samscam/clocklet/Website/images/black-sideon.png

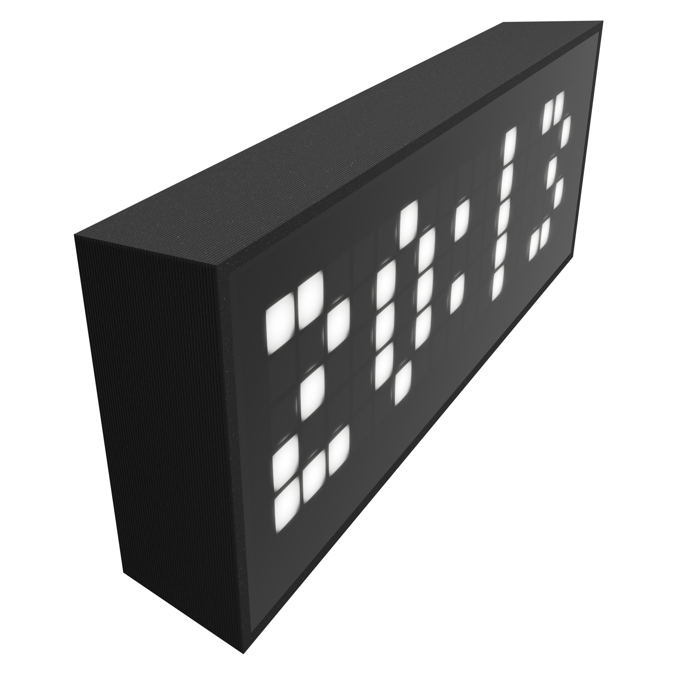
Website/images/black-sideon.png
