samscam/clocklet/Website/images/clocklet5-black-masked.png

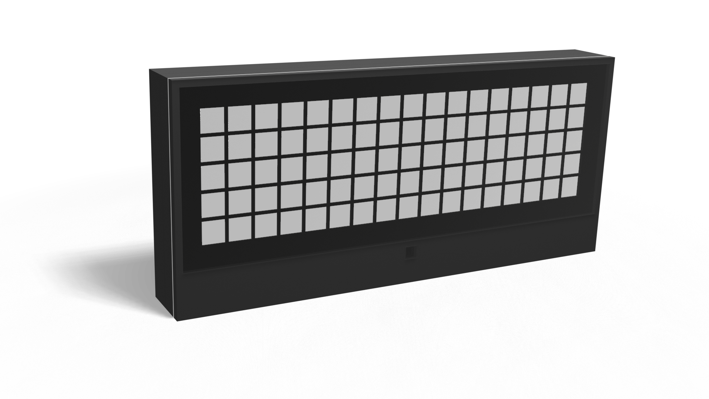
Website/images/clocklet5-black-masked.png
