samscam/clocklet/Website/images/clocklet5-black-time.png

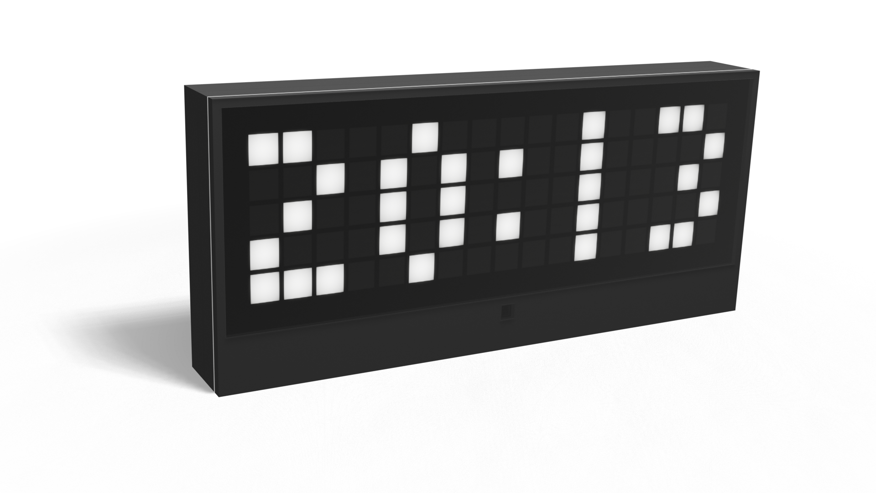
Website/images/clocklet5-black-time.png
