samscam/clocklet/Website/images/clocklet5-final-hello.png

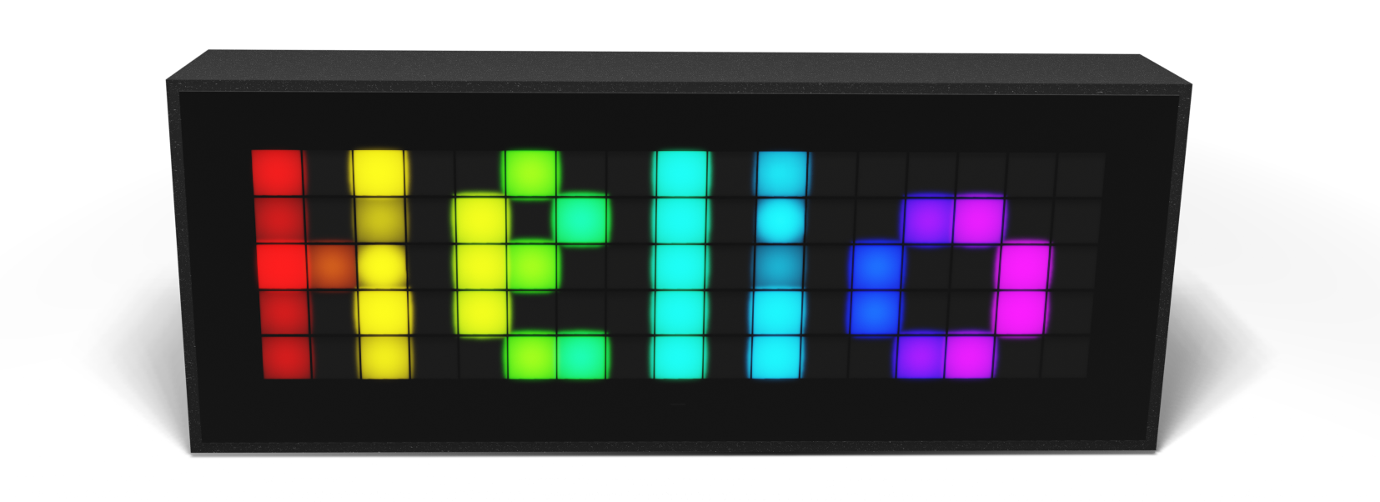
Website/images/clocklet5-final-hello.png
