samscam/clocklet/Embedded/src/TimeThings/Zones.h

#pragma once

const char* zones[] = {
"Africa/Abidjan","GMT0",
"Africa/Accra","GMT0",
"Africa/Addis_Ababa","EAT-3",
"Africa/Algiers","CET-1",
"Africa/Asmara","EAT-3",
"Africa/Bamako","GMT0",
"Africa/Bangui","WAT-1",
"Africa/Banjul","GMT0",
"Africa/Bissau","GMT0",
"Africa/Blantyre","CAT-2",
"Africa/Brazzaville","WAT-1",
"Africa/Bujumbura","CAT-2",
"Africa/Cairo","EET-2",
"Africa/Casablanca","FAKE-1",
"Africa/Ceuta","CET-1CEST,M3.5.0,M10.5.0/3",
"Africa/Conakry","GMT0",
"Africa/Dakar","GMT0",
"Africa/Dar_es_Salaam","EAT-3",
"Africa/Djibouti","EAT-3",
"Africa/Douala","WAT-1",
"Africa/El_Aaiun","FAKE-1",
"Africa/Freetown","GMT0",
"Africa/Gaborone","CAT-2",
"Africa/Harare","CAT-2",
"Africa/Johannesburg","SAST-2",
"Africa/Juba","EAT-3",
"Africa/Kampala","EAT-3",
"Africa/Khartoum","CAT-2",
"Africa/Kigali","CAT-2",
"Africa/Kinshasa","WAT-1",
"Africa/Lagos","WAT-1",
"Africa/Libreville","WAT-1",
"Africa/Lome","GMT0",
"Africa/Luanda","WAT-1",
"Africa/Lubumbashi","CAT-2",
"Africa/Lusaka","CAT-2",
"Africa/Malabo","WAT-1",
"Africa/Maputo","CAT-2",
"Africa/Maseru","SAST-2",
"Africa/Mbabane","SAST-2",
"Africa/Mogadishu","EAT-3",
"Africa/Monrovia","GMT0",
"Africa/Nairobi","EAT-3",
"Africa/Ndjamena","WAT-1",
"Africa/Niamey","WAT-1",
"Africa/Nouakchott","GMT0",
"Africa/Ouagadougou","GMT0",
"Africa/Porto-Novo","WAT-1",
"Africa/Sao_Tome","GMT0",
"Africa/Tripoli","EET-2",
"Africa/Tunis","CET-1",
"Africa/Windhoek","CAT-2",
"America/Adak","HST10HDT,M3.2.0,M11.1.0",
"America/Anchorage","AKST9AKDT,M3.2.0,M11.1.0",
"America/Anguilla","AST4",
"America/Antigua","AST4",
"America/Araguaina","FAKE3",
"America/Argentina/Buenos_Aires","FAKE3",
"America/Argentina/Catamarca","FAKE3",
"America/Argentina/Cordoba","FAKE3",
"America/Argentina/Jujuy","FAKE3",
"America/Argentina/La_Rioja","FAKE3",
"America/Argentina/Mendoza","FAKE3",
"America/Argentina/Rio_Gallegos","FAKE3",
"America/Argentina/Salta","FAKE3",
"America/Argentina/San_Juan","FAKE3",
"America/Argentina/San_Luis","FAKE3",
"America/Argentina/Tucuman","FAKE3",
"America/Argentina/Ushuaia","FAKE3",
"America/Aruba","AST4",
"America/Asuncion","FAKE4FAKE,M10.1.0/0,M3.4.0/0",
"America/Atikokan","EST5",
"America/Bahia","FAKE3",
"America/Bahia_Banderas","CST6CDT,M4.1.0,M10.5.0",
"America/Barbados","AST4",
"America/Belem","FAKE3",
"America/Belize","CST6",
"America/Blanc-Sablon","AST4",
"America/Boa_Vista","FAKE4",
"America/Bogota","FAKE5",
"America/Boise","MST7MDT,M3.2.0,M11.1.0",
"America/Cambridge_Bay","MST7MDT,M3.2.0,M11.1.0",
"America/Campo_Grande","FAKE4",
"America/Cancun","EST5",
"America/Caracas","FAKE4",
"America/Cayenne","FAKE3",
"America/Cayman","EST5",
"America/Chicago","CST6CDT,M3.2.0,M11.1.0",
"America/Chihuahua","MST7MDT,M4.1.0,M10.5.0",
"America/Costa_Rica","CST6",
"America/Creston","MST7",
"America/Cuiaba","FAKE4",
"America/Curacao","AST4",
"America/Danmarkshavn","GMT0",
"America/Dawson","MST7",
"America/Dawson_Creek","MST7",
"America/Denver","MST7MDT,M3.2.0,M11.1.0",
"America/Detroit","EST5EDT,M3.2.0,M11.1.0",
"America/Dominica","AST4",
"America/Edmonton","MST7MDT,M3.2.0,M11.1.0",
"America/Eirunepe","FAKE5",
"America/El_Salvador","CST6",
"America/Fortaleza","FAKE3",
"America/Fort_Nelson","MST7",
"America/Glace_Bay","AST4ADT,M3.2.0,M11.1.0",
"America/Godthab","FAKE3FAKE,M3.5.0/-2,M10.5.0/-1",
"America/Goose_Bay","AST4ADT,M3.2.0,M11.1.0",
"America/Grand_Turk","EST5EDT,M3.2.0,M11.1.0",
"America/Grenada","AST4",
"America/Guadeloupe","AST4",
"America/Guatemala","CST6",
"America/Guayaquil","FAKE5",
"America/Guyana","FAKE4",
"America/Halifax","AST4ADT,M3.2.0,M11.1.0",
"America/Havana","CST5CDT,M3.2.0/0,M11.1.0/1",
"America/Hermosillo","MST7",
"America/Indiana/Indianapolis","EST5EDT,M3.2.0,M11.1.0",
"America/Indiana/Knox","CST6CDT,M3.2.0,M11.1.0",
"America/Indiana/Marengo","EST5EDT,M3.2.0,M11.1.0",
"America/Indiana/Petersburg","EST5EDT,M3.2.0,M11.1.0",
"America/Indiana/Tell_City","CST6CDT,M3.2.0,M11.1.0",
"America/Indiana/Vevay","EST5EDT,M3.2.0,M11.1.0",
"America/Indiana/Vincennes","EST5EDT,M3.2.0,M11.1.0",
"America/Indiana/Winamac","EST5EDT,M3.2.0,M11.1.0",
"America/Inuvik","MST7MDT,M3.2.0,M11.1.0",
"America/Iqaluit","EST5EDT,M3.2.0,M11.1.0",
"America/Jamaica","EST5",
"America/Juneau","AKST9AKDT,M3.2.0,M11.1.0",
"America/Kentucky/Louisville","EST5EDT,M3.2.0,M11.1.0",
"America/Kentucky/Monticello","EST5EDT,M3.2.0,M11.1.0",
"America/Kralendijk","AST4",
"America/La_Paz","FAKE4",
"America/Lima","FAKE5",
"America/Los_Angeles","PST8PDT,M3.2.0,M11.1.0",
"America/Lower_Princes","AST4",
"America/Maceio","FAKE3",
"America/Managua","CST6",
"America/Manaus","FAKE4",
"America/Marigot","AST4",
"America/Martinique","AST4",
"America/Matamoros","CST6CDT,M3.2.0,M11.1.0",
"America/Mazatlan","MST7MDT,M4.1.0,M10.5.0",
"America/Menominee","CST6CDT,M3.2.0,M11.1.0",
"America/Merida","CST6CDT,M4.1.0,M10.5.0",
"America/Metlakatla","AKST9AKDT,M3.2.0,M11.1.0",
"America/Mexico_City","CST6CDT,M4.1.0,M10.5.0",
"America/Miquelon","FAKE3FAKE,M3.2.0,M11.1.0",
"America/Moncton","AST4ADT,M3.2.0,M11.1.0",
"America/Monterrey","CST6CDT,M4.1.0,M10.5.0",
"America/Montevideo","FAKE3",
"America/Montreal","EST5EDT,M3.2.0,M11.1.0",
"America/Montserrat","AST4",
"America/Nassau","EST5EDT,M3.2.0,M11.1.0",
"America/New_York","EST5EDT,M3.2.0,M11.1.0",
"America/Nipigon","EST5EDT,M3.2.0,M11.1.0",
"America/Nome","AKST9AKDT,M3.2.0,M11.1.0",
"America/Noronha","FAKE2",
"America/North_Dakota/Beulah","CST6CDT,M3.2.0,M11.1.0",
"America/North_Dakota/Center","CST6CDT,M3.2.0,M11.1.0",
"America/North_Dakota/New_Salem","CST6CDT,M3.2.0,M11.1.0",
"America/Ojinaga","MST7MDT,M3.2.0,M11.1.0",
"America/Panama","EST5",
"America/Pangnirtung","EST5EDT,M3.2.0,M11.1.0",
"America/Paramaribo","FAKE3",
"America/Phoenix","MST7",
"America/Port-au-Prince","EST5EDT,M3.2.0,M11.1.0",
"America/Port_of_Spain","AST4",
"America/Porto_Velho","FAKE4",
"America/Puerto_Rico","AST4",
"America/Punta_Arenas","FAKE3",
"America/Rainy_River","CST6CDT,M3.2.0,M11.1.0",
"America/Rankin_Inlet","CST6CDT,M3.2.0,M11.1.0",
"America/Recife","FAKE3",
"America/Regina","CST6",
"America/Resolute","CST6CDT,M3.2.0,M11.1.0",
"America/Rio_Branco","FAKE5",
"America/Santarem","FAKE3",
"America/Santiago","FAKE4FAKE,M9.1.6/24,M4.1.6/24",
"America/Santo_Domingo","AST4",
"America/Sao_Paulo","FAKE3",
"America/Scoresbysund","FAKE1FAKE,M3.5.0/0,M10.5.0/1",
"America/Sitka","AKST9AKDT,M3.2.0,M11.1.0",
"America/St_Barthelemy","AST4",
"America/St_Johns","NST3:30NDT,M3.2.0,M11.1.0",
"America/St_Kitts","AST4",
"America/St_Lucia","AST4",
"America/St_Thomas","AST4",
"America/St_Vincent","AST4",
"America/Swift_Current","CST6",
"America/Tegucigalpa","CST6",
"America/Thule","AST4ADT,M3.2.0,M11.1.0",
"America/Thunder_Bay","EST5EDT,M3.2.0,M11.1.0",
"America/Tijuana","PST8PDT,M3.2.0,M11.1.0",
"America/Toronto","EST5EDT,M3.2.0,M11.1.0",
"America/Tortola","AST4",
"America/Vancouver","PST8PDT,M3.2.0,M11.1.0",
"America/Whitehorse","MST7",
"America/Winnipeg","CST6CDT,M3.2.0,M11.1.0",
"America/Yakutat","AKST9AKDT,M3.2.0,M11.1.0",
"America/Yellowknife","MST7MDT,M3.2.0,M11.1.0",
"Antarctica/Casey","FAKE-8",
"Antarctica/Davis","FAKE-7",
"Antarctica/DumontDUrville","FAKE-10",
"Antarctica/Macquarie","FAKE-11",
"Antarctica/Mawson","FAKE-5",
"Antarctica/McMurdo","NZST-12NZDT,M9.5.0,M4.1.0/3",
"Antarctica/Palmer","FAKE3",
"Antarctica/Rothera","FAKE3",
"Antarctica/Syowa","FAKE-3",
"Antarctica/Troll","FAKE0FAKE-2,M3.5.0/1,M10.5.0/3",
"Antarctica/Vostok","FAKE-6",
"Arctic/Longyearbyen","CET-1CEST,M3.5.0,M10.5.0/3",
"Asia/Aden","FAKE-3",
"Asia/Almaty","FAKE-6",
"Asia/Amman","EET-2EEST,M3.5.4/24,M10.5.5/1",
"Asia/Anadyr","FAKE-12",
"Asia/Aqtau","FAKE-5",
"Asia/Aqtobe","FAKE-5",
"Asia/Ashgabat","FAKE-5",
"Asia/Atyrau","FAKE-5",
"Asia/Baghdad","FAKE-3",
"Asia/Bahrain","FAKE-3",
"Asia/Baku","FAKE-4",
"Asia/Bangkok","FAKE-7",
"Asia/Barnaul","FAKE-7",
"Asia/Beirut","EET-2EEST,M3.5.0/0,M10.5.0/0",
"Asia/Bishkek","FAKE-6",
"Asia/Brunei","FAKE-8",
"Asia/Chita","FAKE-9",
"Asia/Choibalsan","FAKE-8",
"Asia/Colombo","FAKE-5:30",
"Asia/Damascus","EET-2EEST,M3.5.5/0,M10.5.5/0",
"Asia/Dhaka","FAKE-6",
"Asia/Dili","FAKE-9",
"Asia/Dubai","FAKE-4",
"Asia/Dushanbe","FAKE-5",
"Asia/Famagusta","EET-2EEST,M3.5.0/3,M10.5.0/4",
"Asia/Gaza","EET-2EEST,M3.5.5/0,M10.5.6/1",
"Asia/Hebron","EET-2EEST,M3.5.5/0,M10.5.6/1",
"Asia/Ho_Chi_Minh","FAKE-7",
"Asia/Hong_Kong","HKT-8",
"Asia/Hovd","FAKE-7",
"Asia/Irkutsk","FAKE-8",
"Asia/Jakarta","WIB-7",
"Asia/Jayapura","WIT-9",
"Asia/Jerusalem","IST-2IDT,M3.4.4/26,M10.5.0",
"Asia/Kabul","FAKE-4:30",
"Asia/Kamchatka","FAKE-12",
"Asia/Karachi","PKT-5",
"Asia/Kathmandu","FAKE-5:45",
"Asia/Khandyga","FAKE-9",
"Asia/Kolkata","IST-5:30",
"Asia/Krasnoyarsk","FAKE-7",
"Asia/Kuala_Lumpur","FAKE-8",
"Asia/Kuching","FAKE-8",
"Asia/Kuwait","FAKE-3",
"Asia/Macau","CST-8",
"Asia/Magadan","FAKE-11",
"Asia/Makassar","WITA-8",
"Asia/Manila","PST-8",
"Asia/Muscat","FAKE-4",
"Asia/Nicosia","EET-2EEST,M3.5.0/3,M10.5.0/4",
"Asia/Novokuznetsk","FAKE-7",
"Asia/Novosibirsk","FAKE-7",
"Asia/Omsk","FAKE-6",
"Asia/Oral","FAKE-5",
"Asia/Phnom_Penh","FAKE-7",
"Asia/Pontianak","WIB-7",
"Asia/Pyongyang","KST-9",
"Asia/Qatar","FAKE-3",
"Asia/Qyzylorda","FAKE-5",
"Asia/Riyadh","FAKE-3",
"Asia/Sakhalin","FAKE-11",
"Asia/Samarkand","FAKE-5",
"Asia/Seoul","KST-9",
"Asia/Shanghai","CST-8",
"Asia/Singapore","FAKE-8",
"Asia/Srednekolymsk","FAKE-11",
"Asia/Taipei","CST-8",
"Asia/Tashkent","FAKE-5",
"Asia/Tbilisi","FAKE-4",
"Asia/Tehran","FAKE-3:30FAKE,J79/24,J263/24",
"Asia/Thimphu","FAKE-6",
"Asia/Tokyo","JST-9",
"Asia/Tomsk","FAKE-7",
"Asia/Ulaanbaatar","FAKE-8",
"Asia/Urumqi","FAKE-6",
"Asia/Ust-Nera","FAKE-10",
"Asia/Vientiane","FAKE-7",
"Asia/Vladivostok","FAKE-10",
"Asia/Yakutsk","FAKE-9",
"Asia/Yangon","FAKE-6:30",
"Asia/Yekaterinburg","FAKE-5",
"Asia/Yerevan","FAKE-4",
"Atlantic/Azores","FAKE1FAKE,M3.5.0/0,M10.5.0/1",
"Atlantic/Bermuda","AST4ADT,M3.2.0,M11.1.0",
"Atlantic/Canary","WET0WEST,M3.5.0/1,M10.5.0",
"Atlantic/Cape_Verde","FAKE1",
"Atlantic/Faroe","WET0WEST,M3.5.0/1,M10.5.0",
"Atlantic/Madeira","WET0WEST,M3.5.0/1,M10.5.0",
"Atlantic/Reykjavik","GMT0",
"Atlantic/South_Georgia","FAKE2",
"Atlantic/Stanley","FAKE3",
"Atlantic/St_Helena","GMT0",
"Australia/Adelaide","ACST-9:30ACDT,M10.1.0,M4.1.0/3",
"Australia/Brisbane","AEST-10",
"Australia/Broken_Hill","ACST-9:30ACDT,M10.1.0,M4.1.0/3",
"Australia/Currie","AEST-10AEDT,M10.1.0,M4.1.0/3",
"Australia/Darwin","ACST-9:30",
"Australia/Eucla","FAKE-8:45",
"Australia/Hobart","AEST-10AEDT,M10.1.0,M4.1.0/3",
"Australia/Lindeman","AEST-10",
"Australia/Lord_Howe","FAKE-10:30FAKE-11,M10.1.0,M4.1.0",
"Australia/Melbourne","AEST-10AEDT,M10.1.0,M4.1.0/3",
"Australia/Perth","AWST-8",
"Australia/Sydney","AEST-10AEDT,M10.1.0,M4.1.0/3",
"Europe/Amsterdam","CET-1CEST,M3.5.0,M10.5.0/3",
"Europe/Andorra","CET-1CEST,M3.5.0,M10.5.0/3",
"Europe/Astrakhan","FAKE-4",
"Europe/Athens","EET-2EEST,M3.5.0/3,M10.5.0/4",
"Europe/Belgrade","CET-1CEST,M3.5.0,M10.5.0/3",
"Europe/Berlin","CET-1CEST,M3.5.0,M10.5.0/3",
"Europe/Bratislava","CET-1CEST,M3.5.0,M10.5.0/3",
"Europe/Brussels","CET-1CEST,M3.5.0,M10.5.0/3",
"Europe/Bucharest","EET-2EEST,M3.5.0/3,M10.5.0/4",
"Europe/Budapest","CET-1CEST,M3.5.0,M10.5.0/3",
"Europe/Busingen","CET-1CEST,M3.5.0,M10.5.0/3",
"Europe/Chisinau","EET-2EEST,M3.5.0,M10.5.0/3",
"Europe/Copenhagen","CET-1CEST,M3.5.0,M10.5.0/3",
"Europe/Dublin","IST-1GMT0,M10.5.0,M3.5.0/1",
"Europe/Gibraltar","CET-1CEST,M3.5.0,M10.5.0/3",
"Europe/Guernsey","GMT0BST,M3.5.0/1,M10.5.0",
"Europe/Helsinki","EET-2EEST,M3.5.0/3,M10.5.0/4",
"Europe/Isle_of_Man","GMT0BST,M3.5.0/1,M10.5.0",
"Europe/Istanbul","FAKE-3",
"Europe/Jersey","GMT0BST,M3.5.0/1,M10.5.0",
"Europe/Kaliningrad","EET-2",
"Europe/Kiev","EET-2EEST,M3.5.0/3,M10.5.0/4",
"Europe/Kirov","FAKE-3",
"Europe/Lisbon","WET0WEST,M3.5.0/1,M10.5.0",
"Europe/Ljubljana","CET-1CEST,M3.5.0,M10.5.0/3",
"Europe/London","GMT0BST,M3.5.0/1,M10.5.0",
"Europe/Luxembourg","CET-1CEST,M3.5.0,M10.5.0/3",
"Europe/Madrid","CET-1CEST,M3.5.0,M10.5.0/3",
"Europe/Malta","CET-1CEST,M3.5.0,M10.5.0/3",
"Europe/Mariehamn","EET-2EEST,M3.5.0/3,M10.5.0/4",
"Europe/Minsk","FAKE-3",
"Europe/Monaco","CET-1CEST,M3.5.0,M10.5.0/3",
"Europe/Moscow","MSK-3",
"Europe/Oslo","CET-1CEST,M3.5.0,M10.5.0/3",
"Europe/Paris","CET-1CEST,M3.5.0,M10.5.0/3",
"Europe/Podgorica","CET-1CEST,M3.5.0,M10.5.0/3",
"Europe/Prague","CET-1CEST,M3.5.0,M10.5.0/3",
"Europe/Riga","EET-2EEST,M3.5.0/3,M10.5.0/4",
"Europe/Rome","CET-1CEST,M3.5.0,M10.5.0/3",
"Europe/Samara","FAKE-4",
"Europe/San_Marino","CET-1CEST,M3.5.0,M10.5.0/3",
"Europe/Sarajevo","CET-1CEST,M3.5.0,M10.5.0/3",
"Europe/Saratov","FAKE-4",
"Europe/Simferopol","MSK-3",
"Europe/Skopje","CET-1CEST,M3.5.0,M10.5.0/3",
"Europe/Sofia","EET-2EEST,M3.5.0/3,M10.5.0/4",
"Europe/Stockholm","CET-1CEST,M3.5.0,M10.5.0/3",
"Europe/Tallinn","EET-2EEST,M3.5.0/3,M10.5.0/4",
"Europe/Tirane","CET-1CEST,M3.5.0,M10.5.0/3",
"Europe/Ulyanovsk","FAKE-4",
"Europe/Uzhgorod","EET-2EEST,M3.5.0/3,M10.5.0/4",
"Europe/Vaduz","CET-1CEST,M3.5.0,M10.5.0/3",
"Europe/Vatican","CET-1CEST,M3.5.0,M10.5.0/3",
"Europe/Vienna","CET-1CEST,M3.5.0,M10.5.0/3",
"Europe/Vilnius","EET-2EEST,M3.5.0/3,M10.5.0/4",
"Europe/Volgograd","FAKE-4",
"Europe/Warsaw","CET-1CEST,M3.5.0,M10.5.0/3",
"Europe/Zagreb","CET-1CEST,M3.5.0,M10.5.0/3",
"Europe/Zaporozhye","EET-2EEST,M3.5.0/3,M10.5.0/4",
"Europe/Zurich","CET-1CEST,M3.5.0,M10.5.0/3",
"Indian/Antananarivo","EAT-3",
"Indian/Chagos","FAKE-6",
"Indian/Christmas","FAKE-7",
"Indian/Cocos","FAKE-6:30",
"Indian/Comoro","EAT-3",
"Indian/Kerguelen","FAKE-5",
"Indian/Mahe","FAKE-4",
"Indian/Maldives","FAKE-5",
"Indian/Mauritius","FAKE-4",
"Indian/Mayotte","EAT-3",
"Indian/Reunion","FAKE-4",
"Pacific/Apia","FAKE-13FAKE,M9.5.0/3,M4.1.0/4",
"Pacific/Auckland","NZST-12NZDT,M9.5.0,M4.1.0/3",
"Pacific/Bougainville","FAKE-11",
"Pacific/Chatham","FAKE-12:45FAKE,M9.5.0/2:45,M4.1.0/3:45",
"Pacific/Chuuk","FAKE-10",
"Pacific/Easter","FAKE6FAKE,M9.1.6/22,M4.1.6/22",
"Pacific/Efate","FAKE-11",
"Pacific/Enderbury","FAKE-13",
"Pacific/Fakaofo","FAKE-13",
"Pacific/Fiji","FAKE-12FAKE,M11.2.0,M1.2.3/99",
"Pacific/Funafuti","FAKE-12",
"Pacific/Galapagos","FAKE6",
"Pacific/Gambier","FAKE9",
"Pacific/Guadalcanal","FAKE-11",
"Pacific/Guam","ChST-10",
"Pacific/Honolulu","HST10",
"Pacific/Kiritimati","FAKE-14",
"Pacific/Kosrae","FAKE-11",
"Pacific/Kwajalein","FAKE-12",
"Pacific/Majuro","FAKE-12",
"Pacific/Marquesas","FAKE9:30",
"Pacific/Midway","SST11",
"Pacific/Nauru","FAKE-12",
"Pacific/Niue","FAKE11",
"Pacific/Norfolk","FAKE-11FAKE,M10.1.0,M4.1.0/3",
"Pacific/Noumea","FAKE-11",
"Pacific/Pago_Pago","SST11",
"Pacific/Palau","FAKE-9",
"Pacific/Pitcairn","FAKE8",
"Pacific/Pohnpei","FAKE-11",
"Pacific/Port_Moresby","FAKE-10",
"Pacific/Rarotonga","FAKE10",
"Pacific/Saipan","ChST-10",
"Pacific/Tahiti","FAKE10",
"Pacific/Tarawa","FAKE-12",
"Pacific/Tongatapu","FAKE-13",
"Pacific/Wake","FAKE-12",
"Pacific/Wallis","FAKE-12",
"Etc/GMT","GMT0",
"Etc/GMT-0","GMT0",
"Etc/GMT-1","FAKE-1",
"Etc/GMT-2","FAKE-2",
"Etc/GMT-3","FAKE-3",
"Etc/GMT-4","FAKE-4",
"Etc/GMT-5","FAKE-5",
"Etc/GMT-6","FAKE-6",
"Etc/GMT-7","FAKE-7",
"Etc/GMT-8","FAKE-8",
"Etc/GMT-9","FAKE-9",
"Etc/GMT-10","FAKE-10",
"Etc/GMT-11","FAKE-11",
"Etc/GMT-12","FAKE-12",
"Etc/GMT-13","FAKE-13",
"Etc/GMT-14","FAKE-14",
"Etc/GMT0","GMT0",
"Etc/GMT+0","GMT0",
"Etc/GMT+1","FAKE1",
"Etc/GMT+2","FAKE2",
"Etc/GMT+3","FAKE3",
"Etc/GMT+4","FAKE4",
"Etc/GMT+5","FAKE5",
"Etc/GMT+6","FAKE6",
"Etc/GMT+7","FAKE7",
"Etc/GMT+8","FAKE8",
"Etc/GMT+9","FAKE9",
"Etc/GMT+10","FAKE10",
"Etc/GMT+11","FAKE11",
"Etc/GMT+12","FAKE12",
"Etc/UCT","UTC0",
"Etc/UTC","UTC0",
"Etc/Greenwich","GMT0",
"Etc/Universal","UTC0",
"Etc/Zulu","UTC0"
};
