samscam/clocklet/Embedded/src/settings.h

#pragma once

#define FPS               60
#define TIME_24_HOUR      true
#define BLINK_SEPARATOR   true
#define SHOW_DATE         false
#define DECIMAL_TIME      false

// MAP FOR PREFERENCES - keeping it here for now...
  // preferences.putString("owner","people");
  // preferences.putString("swmigrev",VERSION) // last fw version used - update after migrations!
  // preferences.putString("casecolour","black");

  // Location
  // preferences.putDouble("lat",0);
  // preferences.putDouble("lng",0);
